GUOMIANRUI/ros_robot_gmr/sw_medol/渲染/untitled.47.jpg

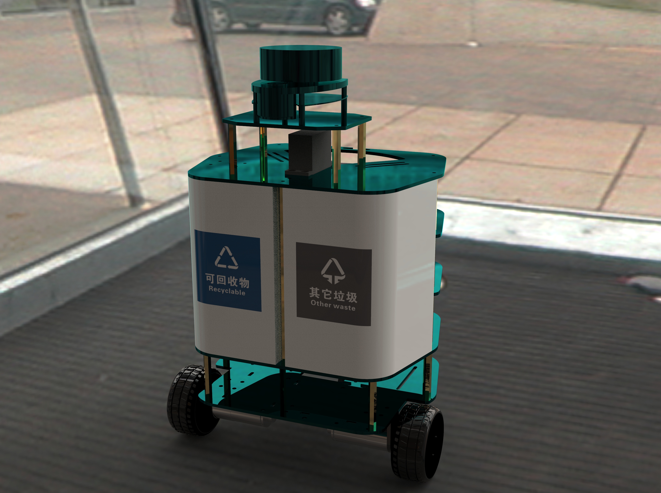
sw_medol/渲染/untitled.47.jpg
