GUOMIANRUI/ros_robot_gmr/sw_medol/1.png

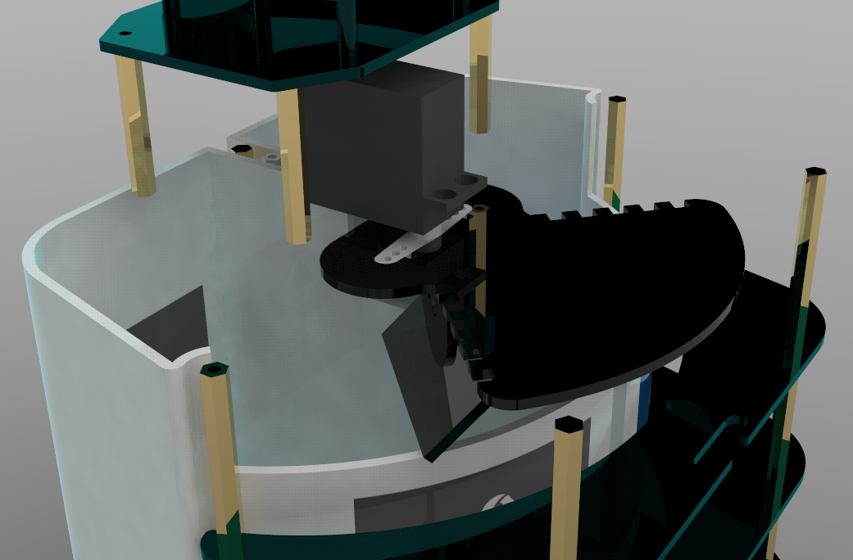
sw_medol/1.png
