GUOMIANRUI/ros_robot_gmr/sw_medol/2.png

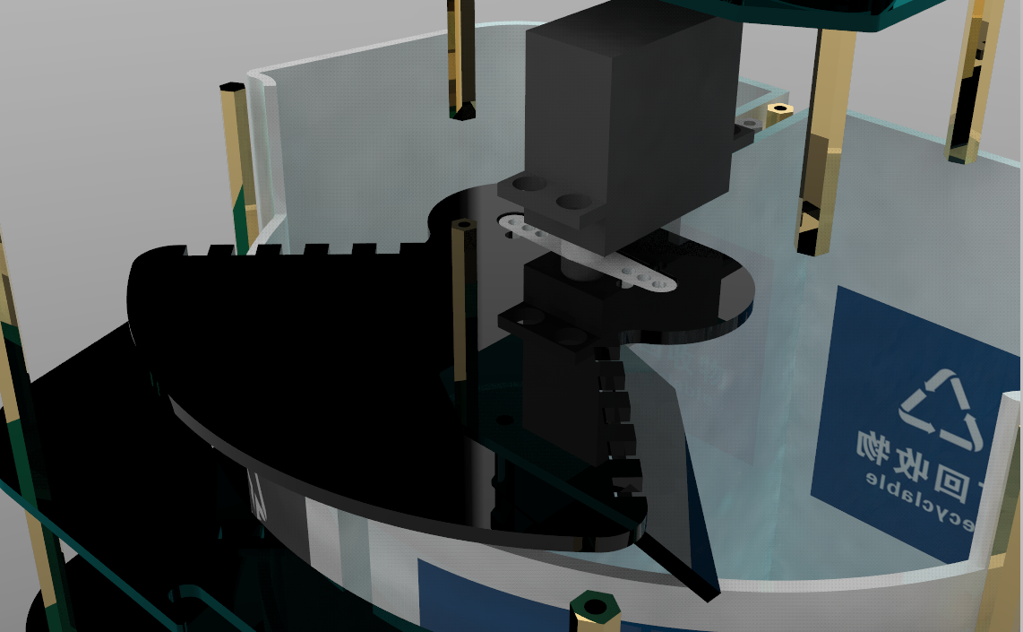
sw_medol/2.png
