GUOMIANRUI/ros_robot_gmr/sw_medol/3.png

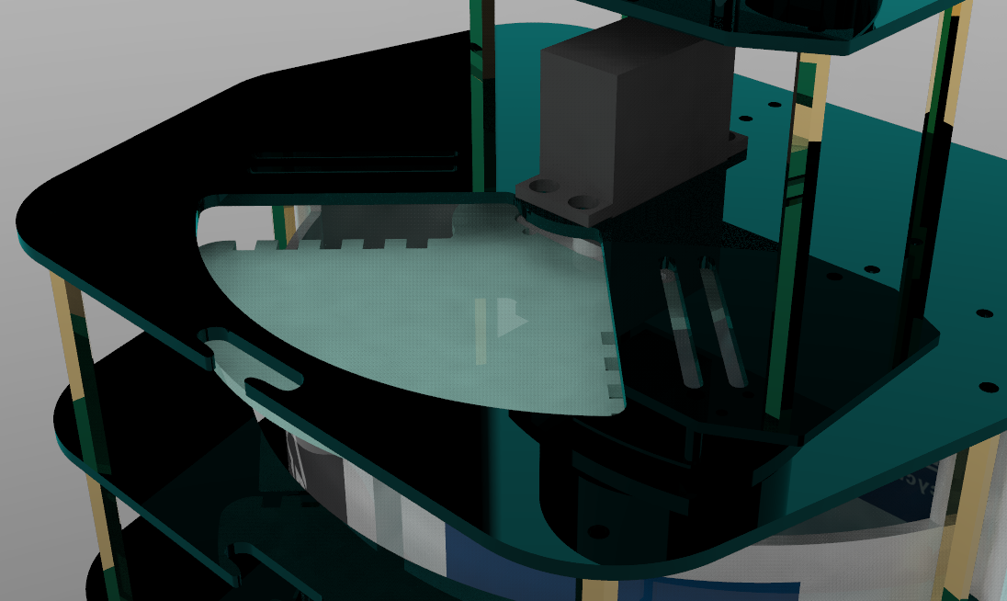
sw_medol/3.png
