GUOMIANRUI/ros_robot_gmr/sw_medol/4.png

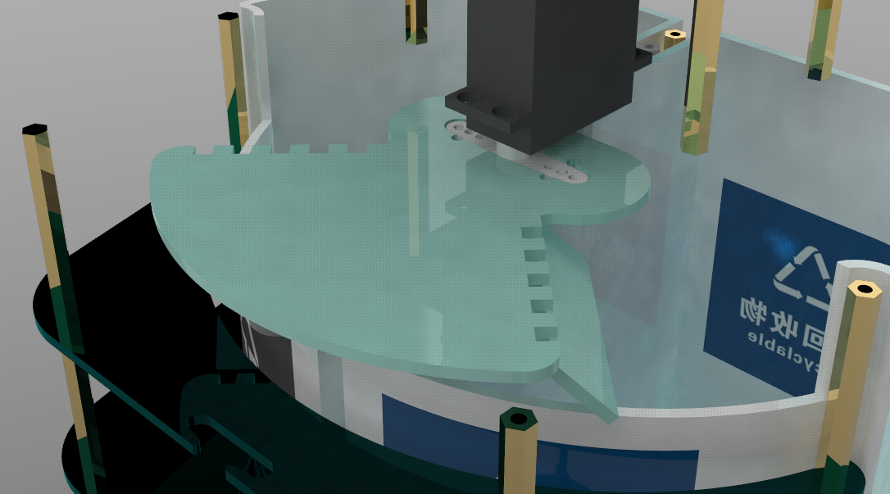
sw_medol/4.png
