GUOMIANRUI/ros_robot_gmr/sw_medol/其他垃圾.png

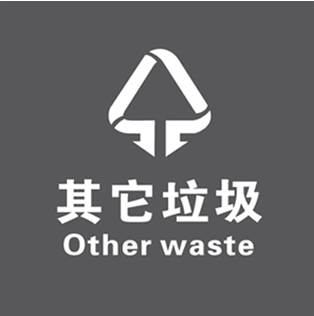
sw_medol/其他垃圾.png
