GUOMIANRUI/ros_robot_gmr/sw_medol/可回收物.png

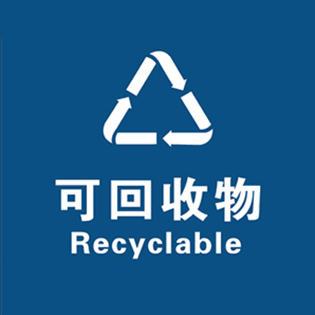
sw_medol/可回收物.png
