GUOMIANRUI/ros_robot_gmr/sw_medol/普通万向轮脚轮/sw caster.2583.jpg

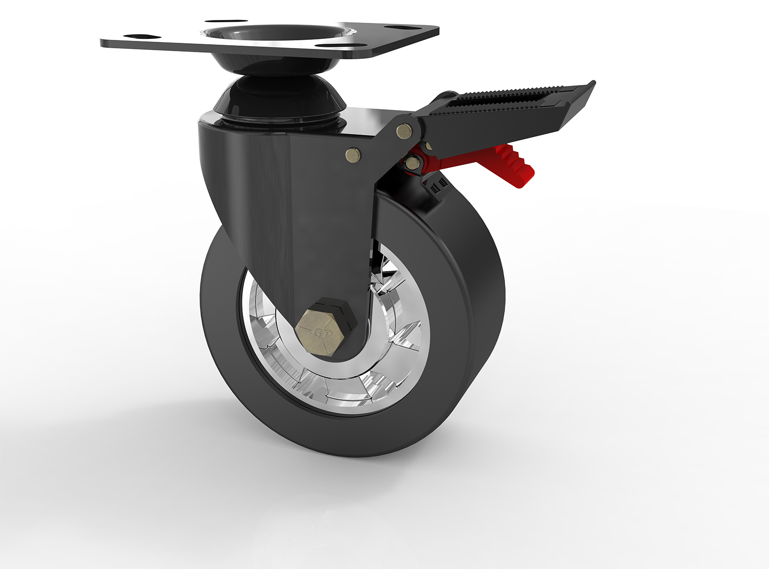
sw_medol/普通万向轮脚轮/sw caster.2583.jpg
