GUOMIANRUI/ros_robot_gmr/ros_robot/catkin_ws/src/jetsonbot_description/meshes/lidar_link.STL

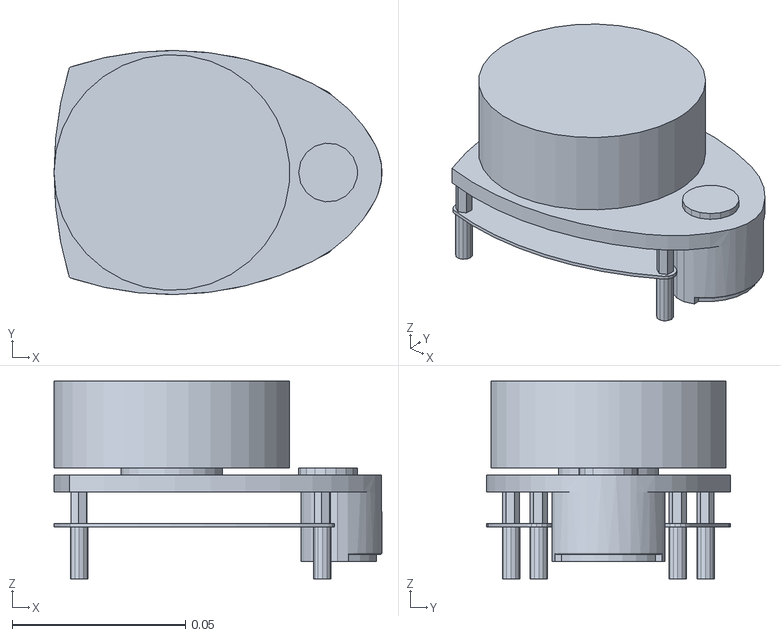
[picture p33: CAD file, 2020-08-31]
ros_robot/catkin_ws/src/jetsonbot_description/meshes/lidar_link.STL
0.0946 x 0.0704 x 0.057
