GUOMIANRUI/ros_robot_gmr/sw_medol/IMU.SLDPRT

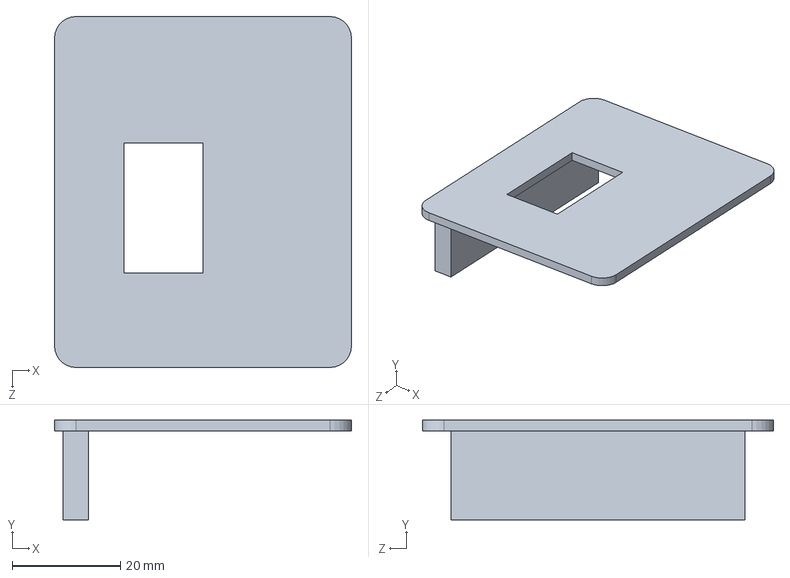
[picture p34: CAD file, 2020-08-26]
sw_medol/IMU.SLDPRT
55.0 x 18.5 x 65.0 mm
