GUOMIANRUI/ros_robot_gmr/sw_medol/新/垃圾桶.SLDPRT

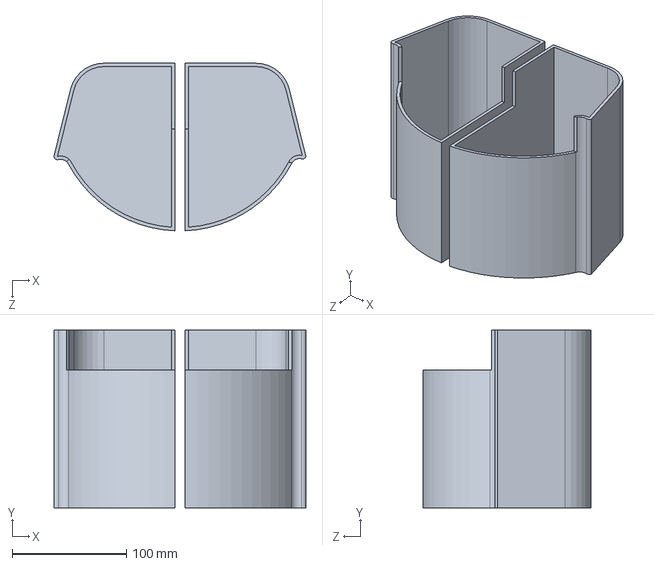
[picture p35: CAD file, 2020-08-26]
sw_medol/新/垃圾桶.SLDPRT
220.9 x 156.0 x 146.9 mm
