GUOMIANRUI/ros_robot_gmr/ros_robot/catkin_ws/src/jetsonbot_description/meshes/imu_link.STL

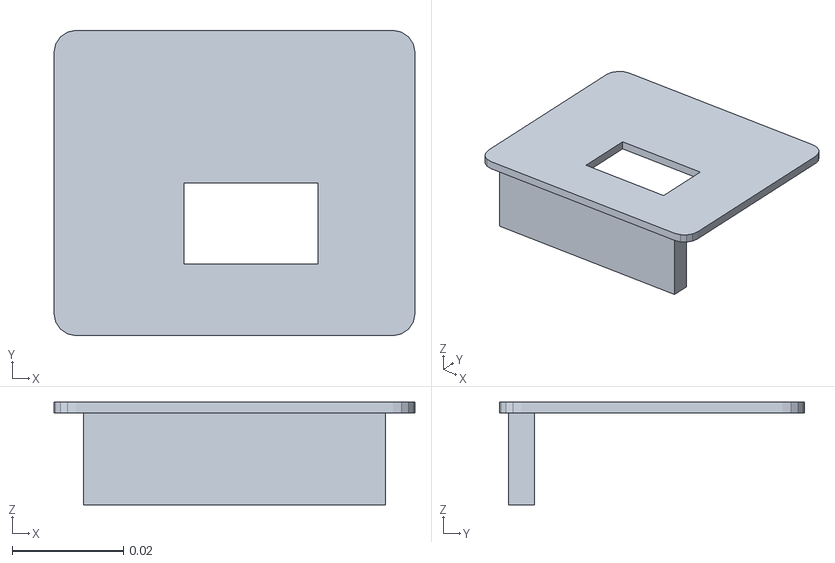
[picture p36: CAD file, 2020-08-31]
ros_robot/catkin_ws/src/jetsonbot_description/meshes/imu_link.STL
0.065 x 0.055 x 0.0185
