GUOMIANRUI/ros_robot_gmr/sw_medol/新/舵机.SLDPRT

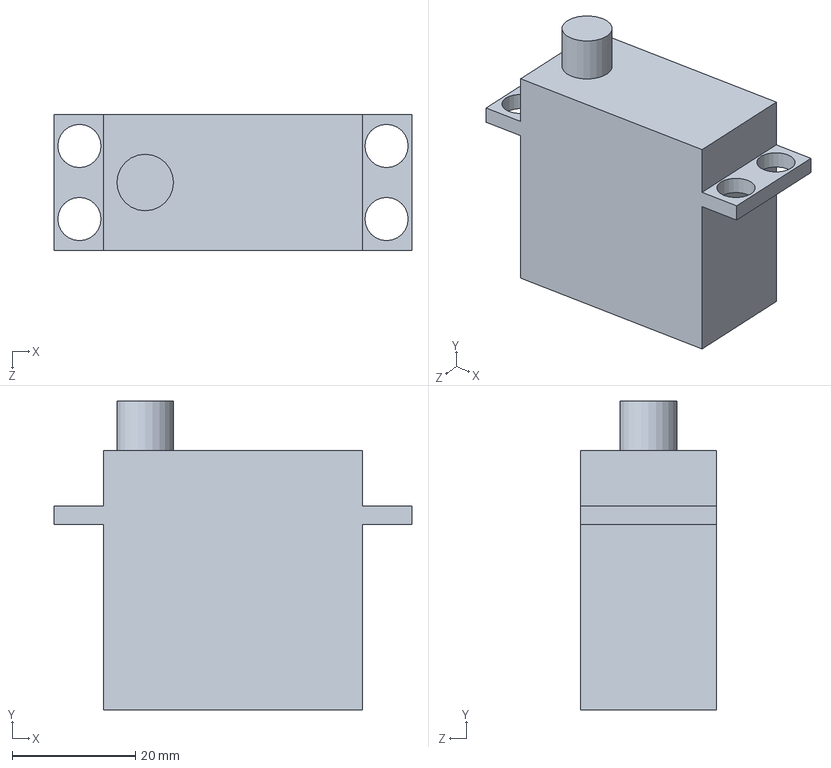
[picture p37: CAD file, 2020-08-26]
sw_medol/新/舵机.SLDPRT
58.0 x 50.0 x 22.0 mm
