GUOMIANRUI/ros_robot_gmr/sw_medol/激光雷达X4.SLDPRT

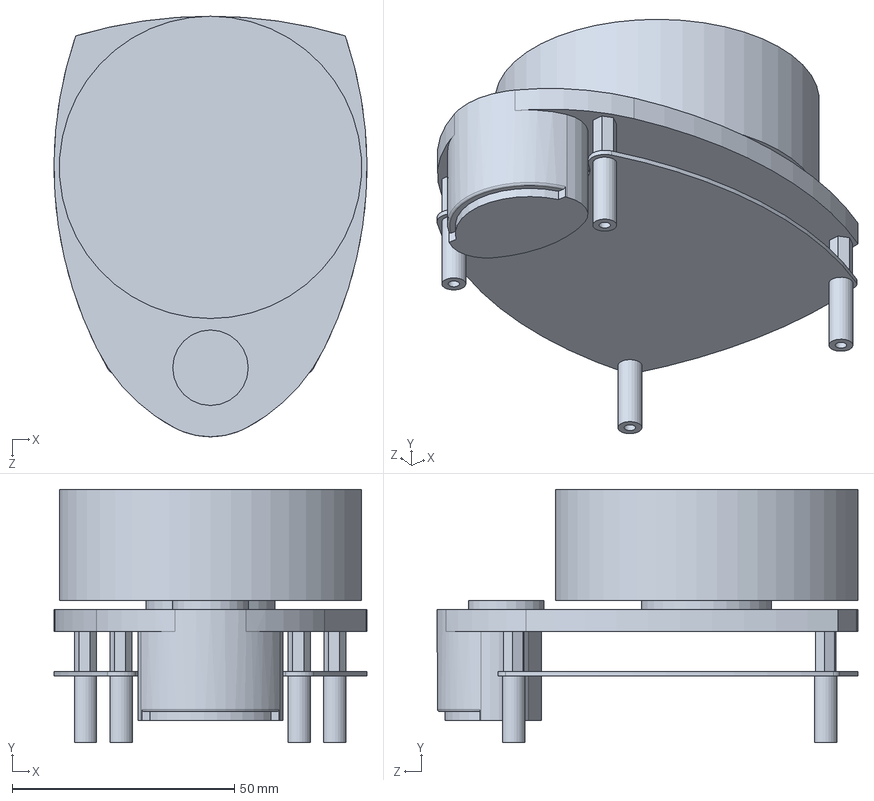
[picture p38: CAD file, 2020-08-26]
sw_medol/激光雷达X4.SLDPRT
70.4 x 57.0 x 94.6 mm
