GUOMIANRUI/ros_robot_gmr/sw_medol/万向轮.SLDPRT

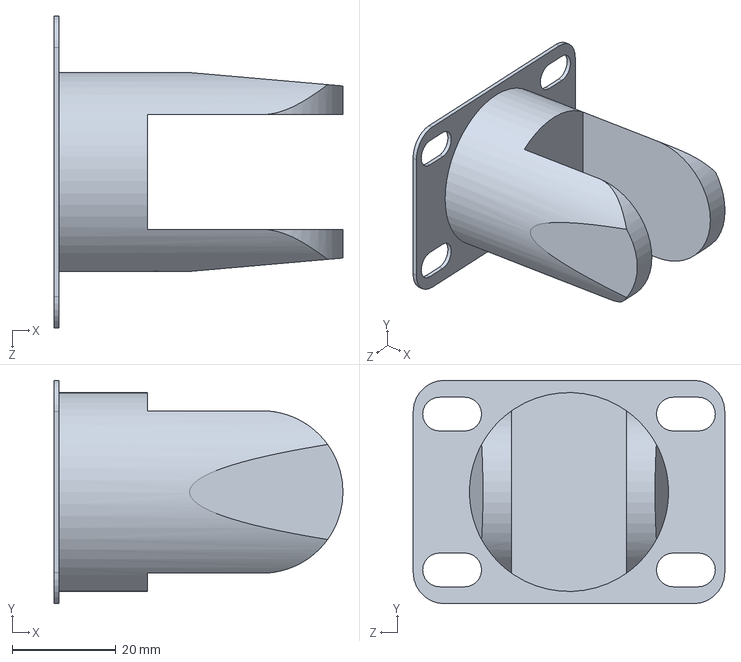
[picture p39: CAD file, 2020-08-26]
sw_medol/万向轮.SLDPRT
55.6 x 43.0 x 60.0 mm
