GUOMIANRUI/ros_robot_gmr/sw_medol/万向轮2.SLDPRT

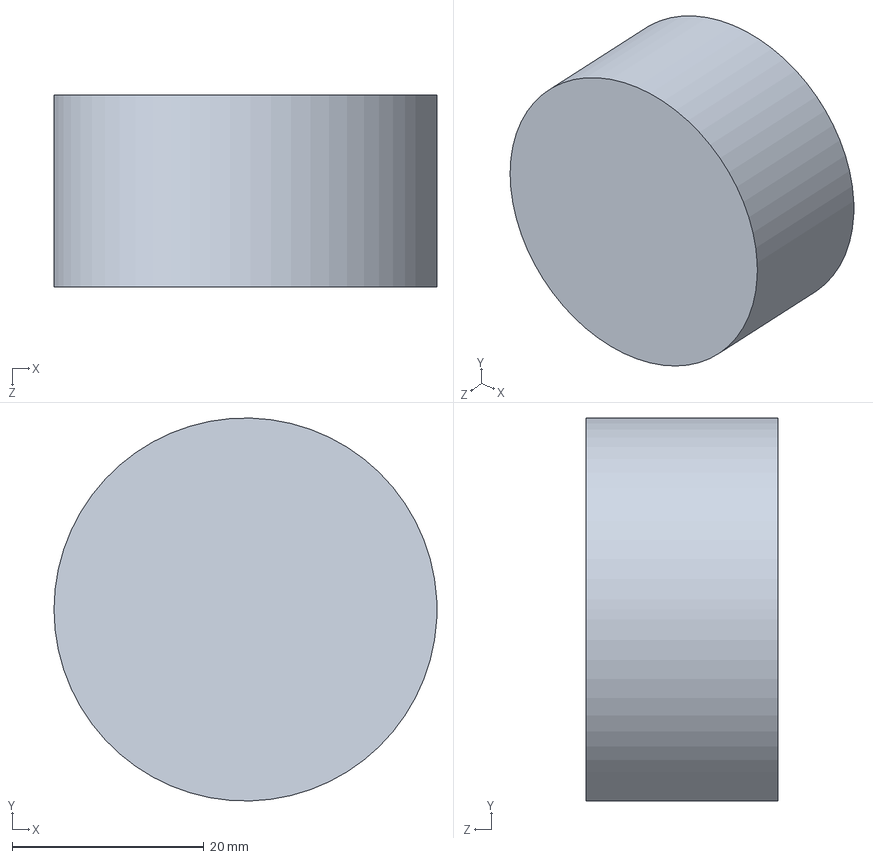
[picture p40: CAD file, 2020-08-26]
sw_medol/万向轮2.SLDPRT
40.0 x 40.0 x 20.0 mm
