GUOMIANRUI/ros_robot_gmr/sw_medol/新/乘物2.SLDPRT

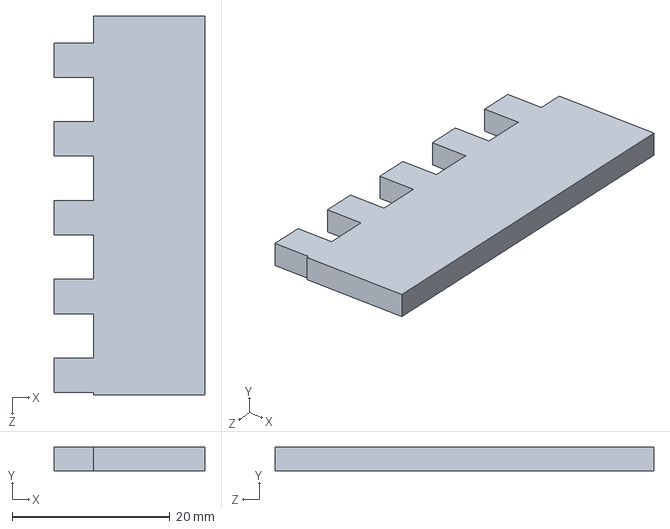
[picture p41: CAD file, 2020-08-26]
sw_medol/新/乘物2.SLDPRT
19.1 x 3.00 x 48.1 mm
