GUOMIANRUI/ros_robot_gmr/sw_medol/新/底板1.SLDPRT

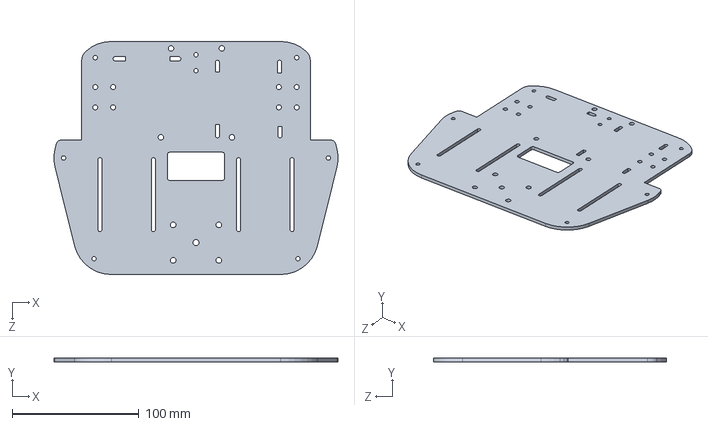
[picture p42: CAD file, 2020-08-26]
sw_medol/新/底板1.SLDPRT
224.1 x 3.00 x 183.9 mm
