GUOMIANRUI/ros_robot_gmr/sw_medol/新/铜柱45.SLDPRT

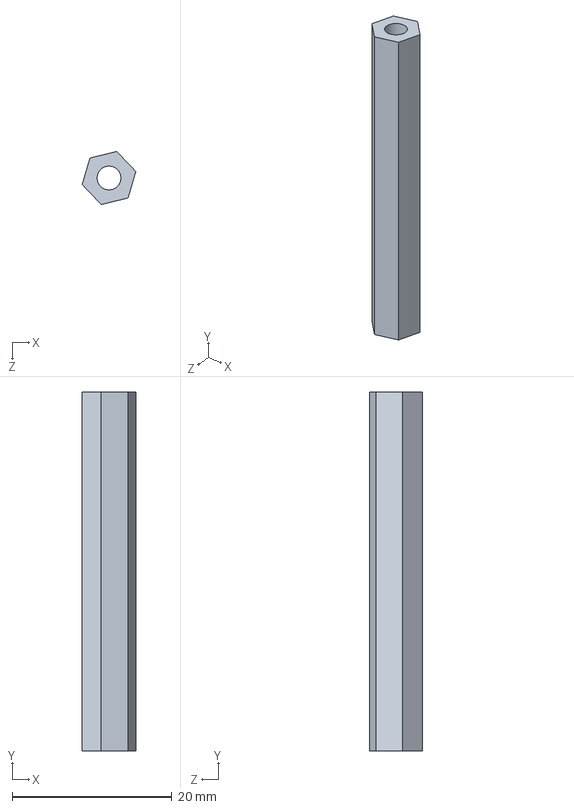
[picture p43: CAD file, 2020-08-26]
sw_medol/新/铜柱45.SLDPRT
6.73 x 45.0 x 6.65 mm
