GUOMIANRUI/ros_robot_gmr/sw_medol/新/底板6.SLDPRT

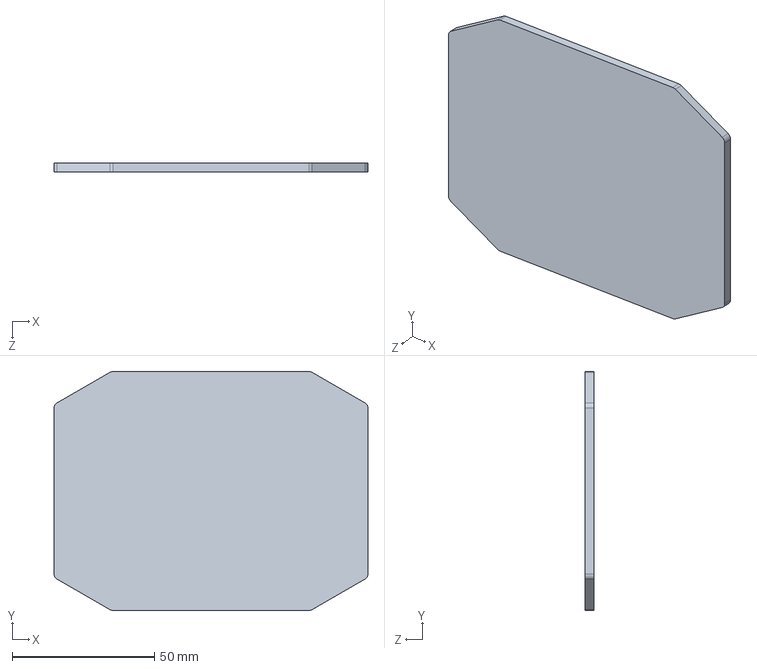
[picture p44: CAD file, 2020-08-26]
sw_medol/新/底板6.SLDPRT
110.3 x 84.0 x 3.00 mm
