GUOMIANRUI/ros_robot_gmr/sw_medol/新/铜柱50.SLDPRT

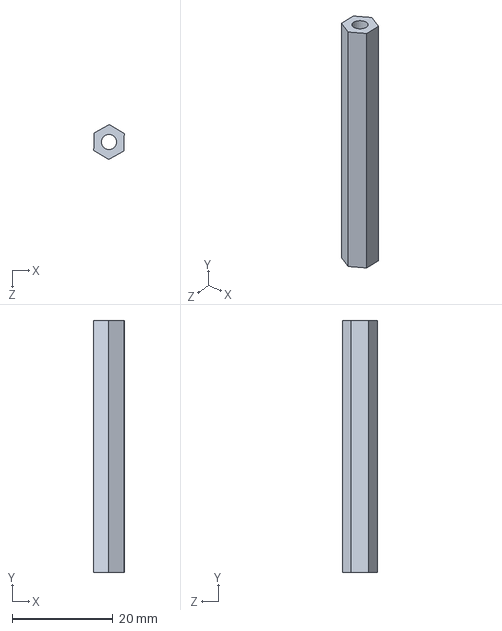
[picture p45: CAD file, 2020-08-26]
sw_medol/新/铜柱50.SLDPRT
6.07 x 50.0 x 6.93 mm
