GUOMIANRUI/ros_robot_gmr/sw_medol/普通万向轮脚轮/sw caster.stp

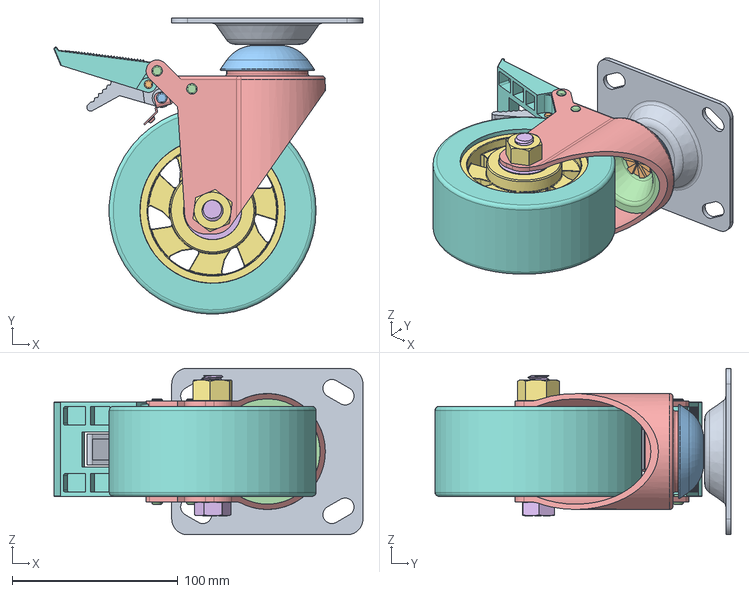
[picture p46: CAD file, 2020-08-26]
sw_medol/普通万向轮脚轮/sw caster.stp
186.2 x 178.4 x 100.3 mm
